ForthgoerGa/Portable-film-digitizer/Image_integration&Post_Processing/Negative_example/norway_split_40_overlap/grid_preview.png

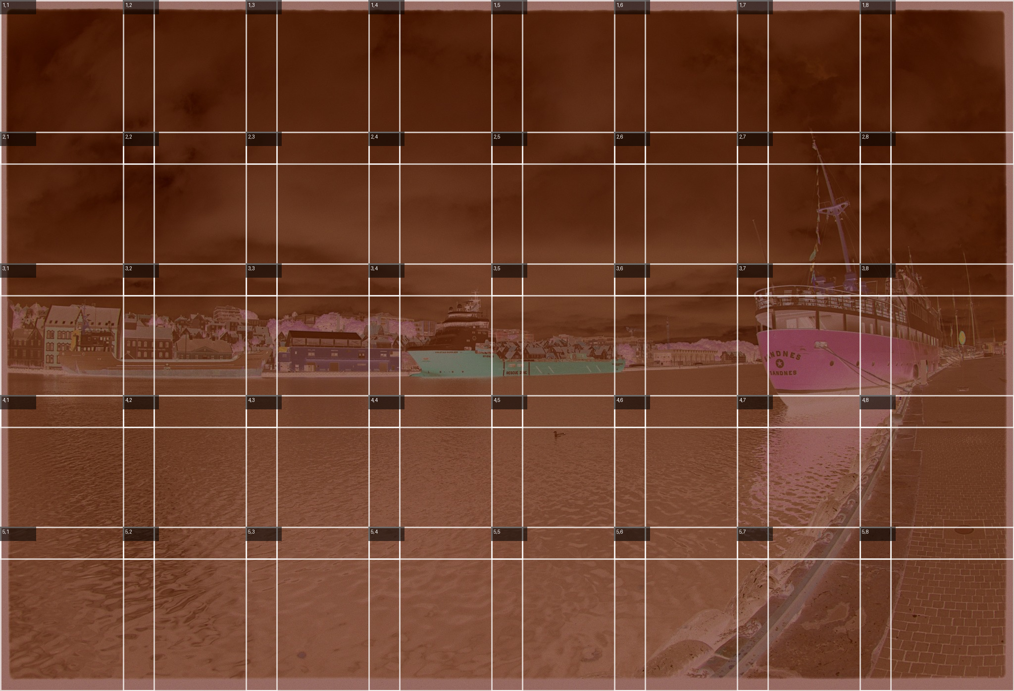
Image_integration&Post_Processing/Negative_example/norway_split_40_overlap/grid_preview.png
