ForthgoerGa/Portable-film-digitizer/Image_integration&Post_Processing/Negative_example/norway_split_40_overlap/tile_r01_c03_03.png

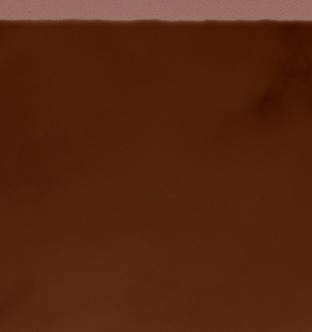
Image_integration&Post_Processing/Negative_example/norway_split_40_overlap/tile_r01_c03_03.png
