ForthgoerGa/Portable-film-digitizer/Image_integration&Post_Processing/Negative_example/norway_split_40_overlap/tile_r01_c08_08.png

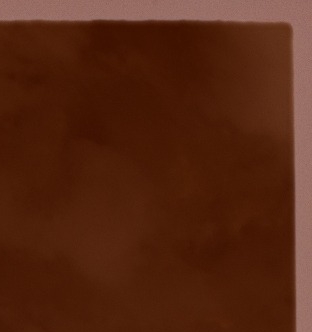
Image_integration&Post_Processing/Negative_example/norway_split_40_overlap/tile_r01_c08_08.png
