ForthgoerGa/Portable-film-digitizer/Image_integration&Post_Processing/Negative_example/norway_split_40_overlap/tile_r04_c01_25.png

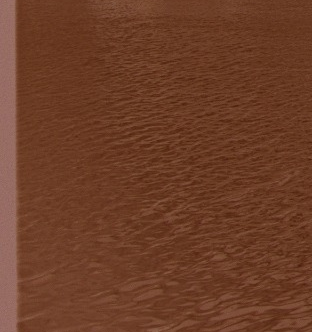
Image_integration&Post_Processing/Negative_example/norway_split_40_overlap/tile_r04_c01_25.png
