ForthgoerGa/Portable-film-digitizer/Image_integration&Post_Processing/Negative_example/norway_split_40_overlap/tile_r04_c03_27.png

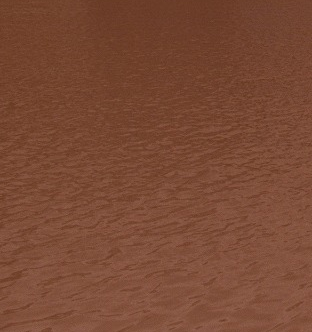
Image_integration&Post_Processing/Negative_example/norway_split_40_overlap/tile_r04_c03_27.png
